camilabga/boberto/CAD/sharp.SLDPRT

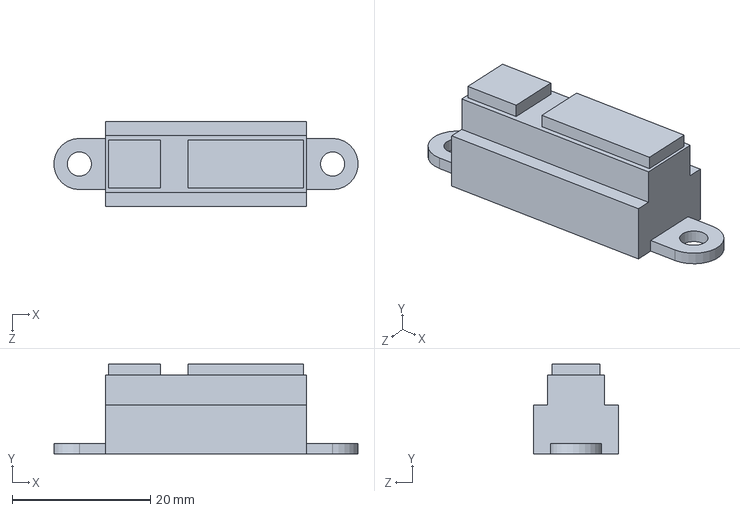
[picture p17: CAD file, 2019-10-31]
CAD/sharp.SLDPRT
43.9 x 13.0 x 12.3 mm
