camilabga/boberto/CAD/suporte barras base.SLDPRT

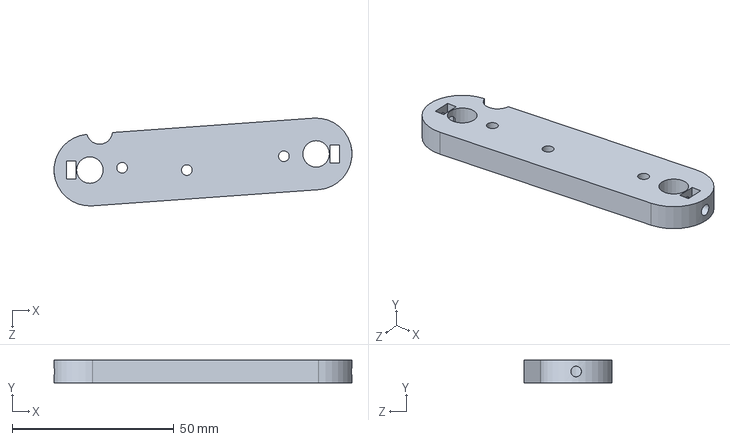
[picture p18: CAD file, 2019-10-31]
CAD/suporte barras base.SLDPRT
92.2 x 7.00 x 27.1 mm
