camilabga/boberto/CAD/suporte fim de curso.SLDPRT

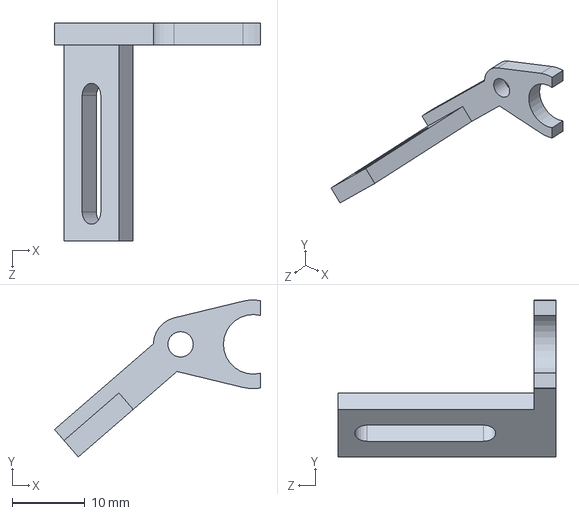
[picture p19: CAD file, 2019-10-31]
CAD/suporte fim de curso.SLDPRT
28.4 x 21.6 x 30.0 mm
