camilabga/boberto/CAD/polia com rolamento.SLDPRT

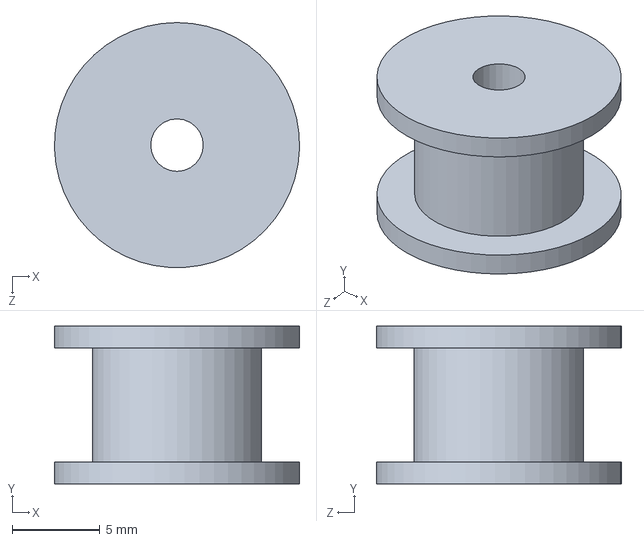
[picture p20: CAD file, 2019-10-31]
CAD/polia com rolamento.SLDPRT
14.0 x 9.00 x 14.0 mm
