camilabga/boberto/CAD/nema17 (30mm altura).SLDPRT

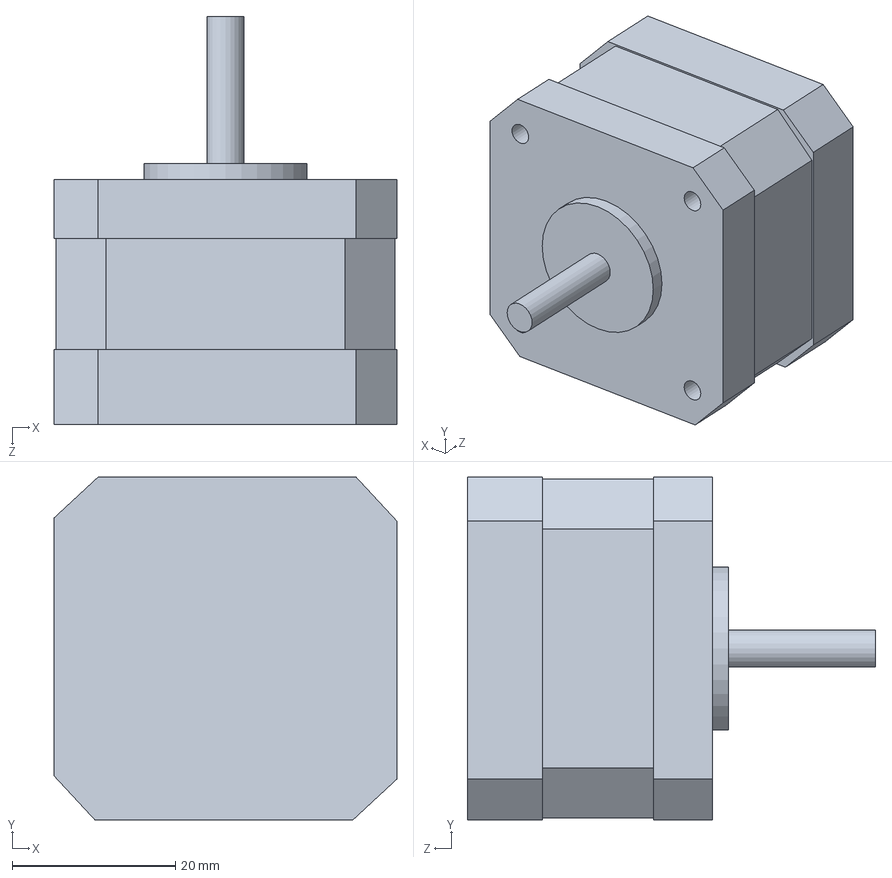
[picture p21: CAD file, 2019-10-31]
CAD/nema17 (30mm altura).SLDPRT
42.0 x 42.0 x 50.0 mm
