camilabga/boberto/CAD/chassis meio.SLDPRT

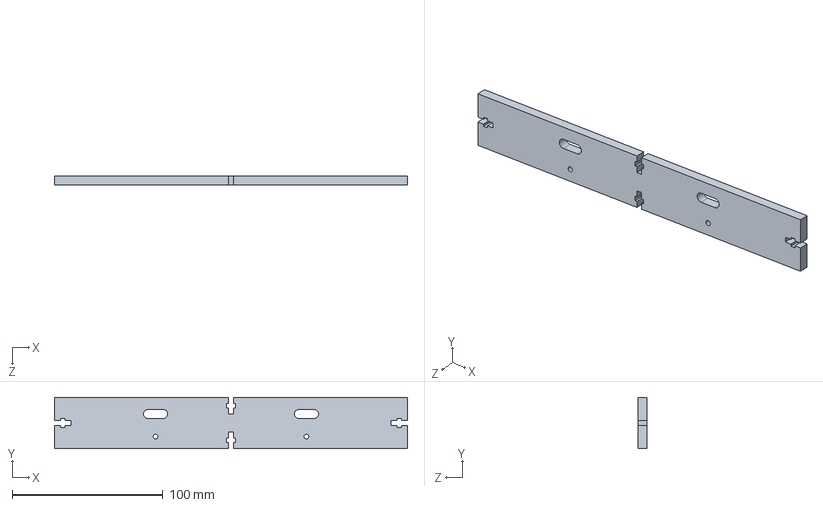
[picture p22: CAD file, 2019-10-31]
CAD/chassis meio.SLDPRT
234.0 x 34.0 x 6.00 mm
