camilabga/boberto/CAD/Servo 9g.SLDPRT

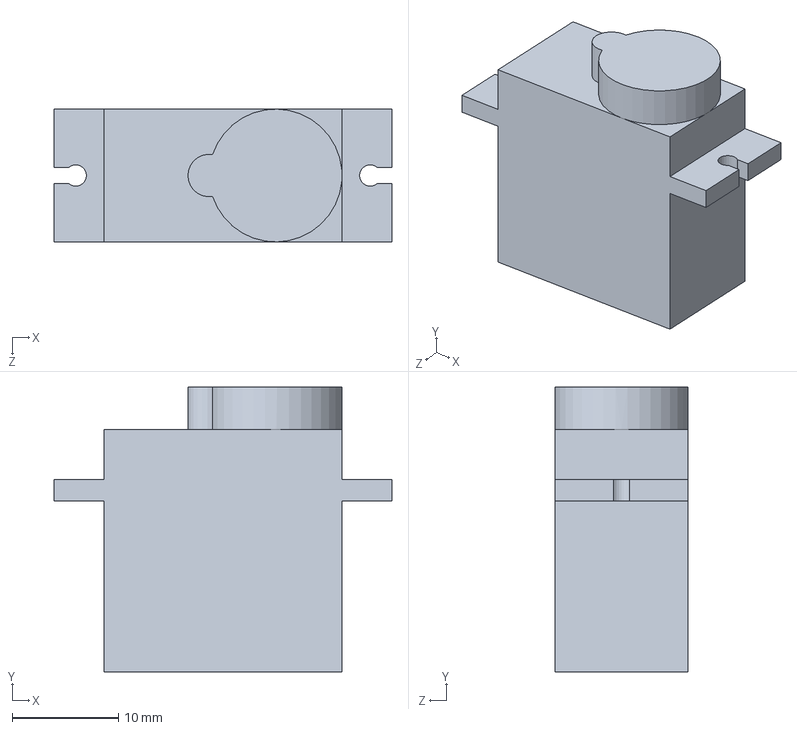
[picture p23: CAD file, 2019-10-31]
CAD/Servo 9g.SLDPRT
31.8 x 26.8 x 12.5 mm
