camilabga/boberto/CAD/motor N20.SLDPRT

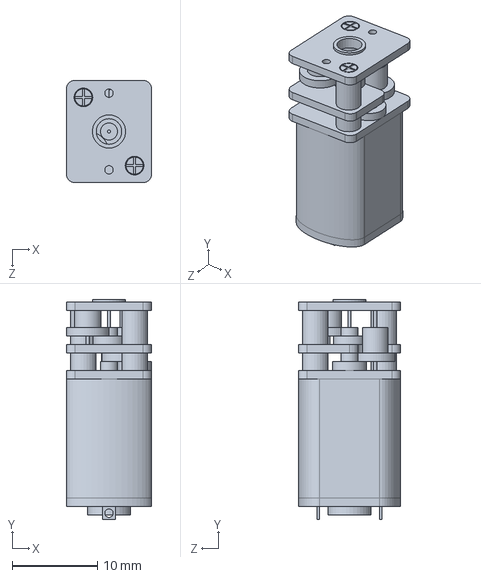
[picture p24: CAD file, 2019-10-31]
CAD/motor N20.SLDPRT
10.0 x 25.8 x 12.0 mm
