camilabga/boberto/CAD/apoio container.SLDPRT

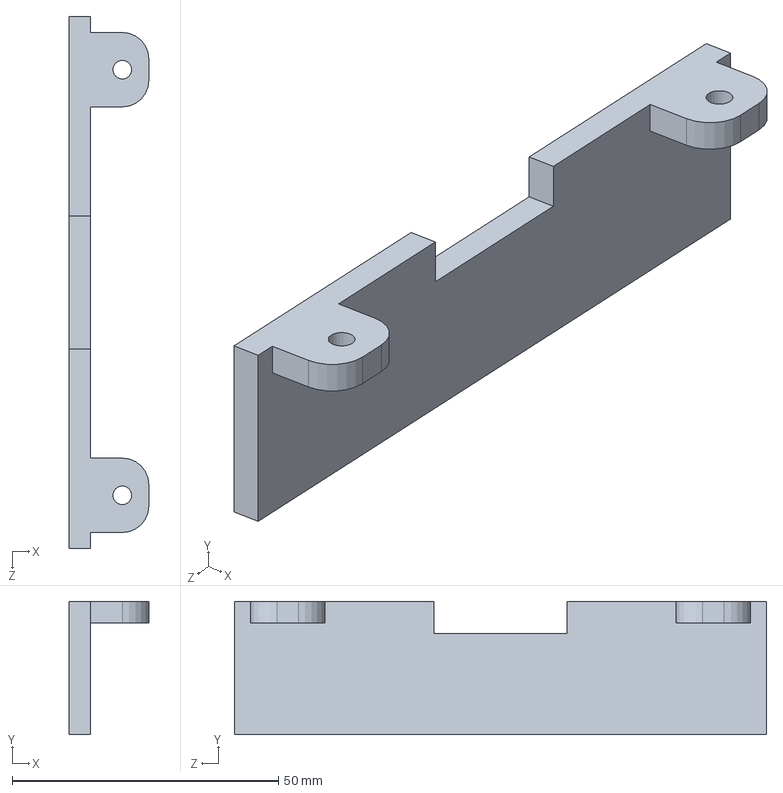
[picture p25: CAD file, 2019-10-31]
CAD/apoio container.SLDPRT
15.0 x 25.0 x 100.0 mm
