camilabga/boberto/CAD/chassis direita.SLDPRT

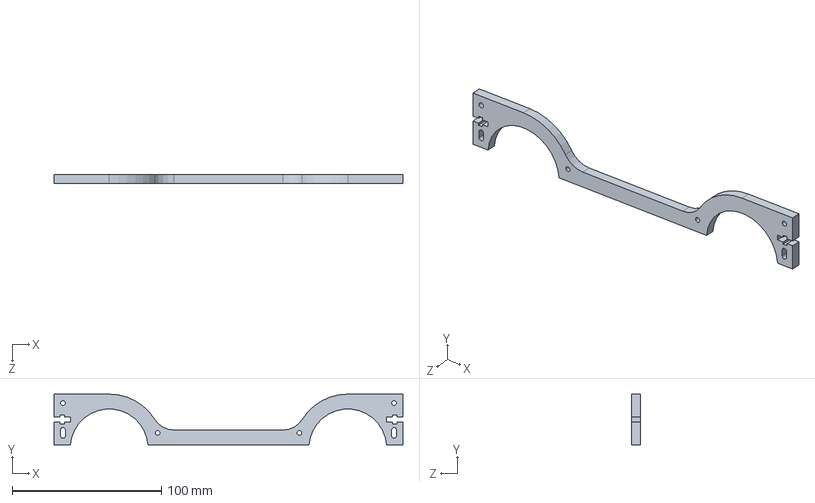
[picture p26: CAD file, 2019-10-31]
CAD/chassis direita.SLDPRT
234.0 x 34.1 x 6.00 mm
