camilabga/boberto/CAD/contrapeso.SLDPRT

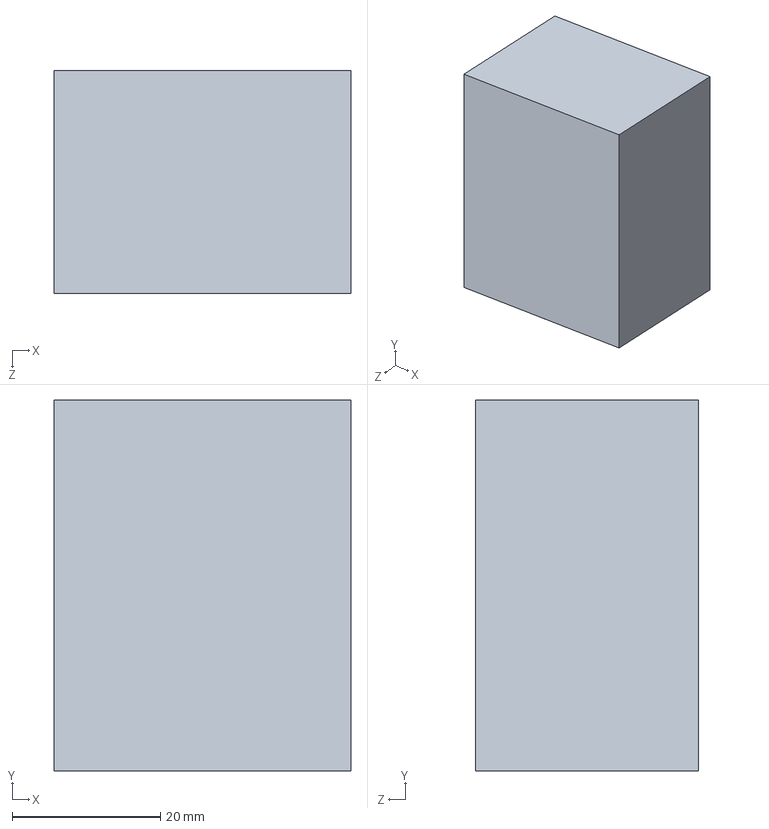
[picture p27: CAD file, 2019-10-31]
CAD/contrapeso.SLDPRT
40.0 x 50.0 x 30.0 mm
