camilabga/boberto/CAD/PCB + arduino.SLDPRT

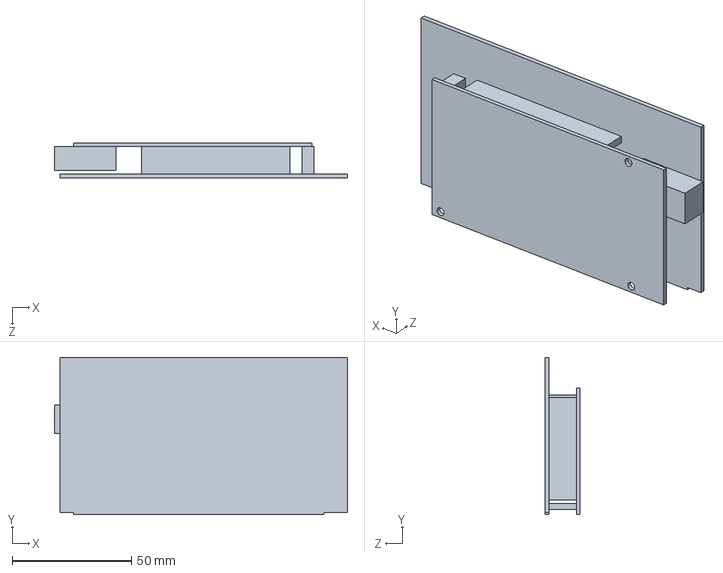
[picture p28: CAD file, 2019-10-31]
CAD/PCB + arduino.SLDPRT
122.9 x 65.9 x 14.8 mm
