camilabga/boberto/CAD/suporte correia.SLDPRT

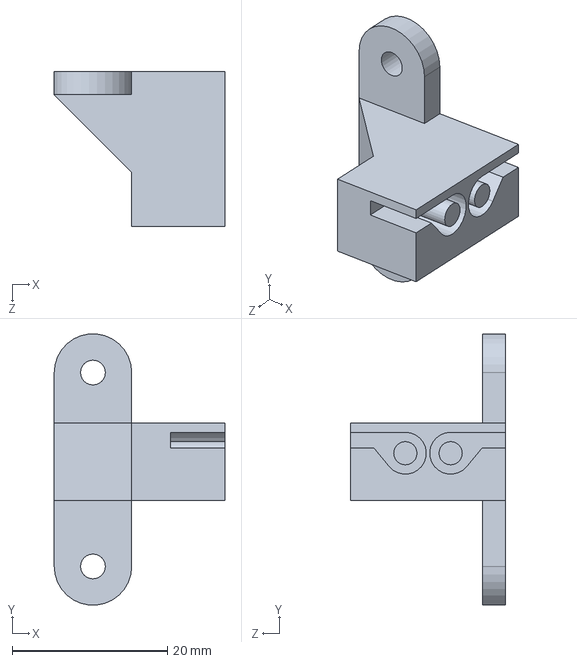
[picture p29: CAD file, 2019-10-31]
CAD/suporte correia.SLDPRT
22.0 x 34.9 x 20.0 mm
