camilabga/boberto/CAD/suporte sensores laterais.SLDPRT

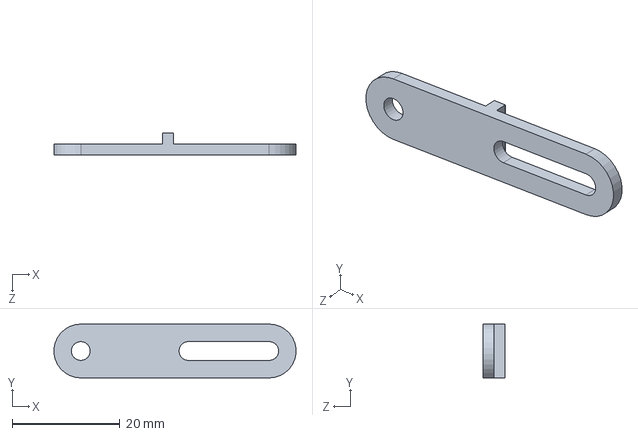
[picture p30: CAD file, 2019-10-31]
CAD/suporte sensores laterais.SLDPRT
44.9 x 10.0 x 4.00 mm
