camilabga/boberto/CAD/chassis.SLDPRT

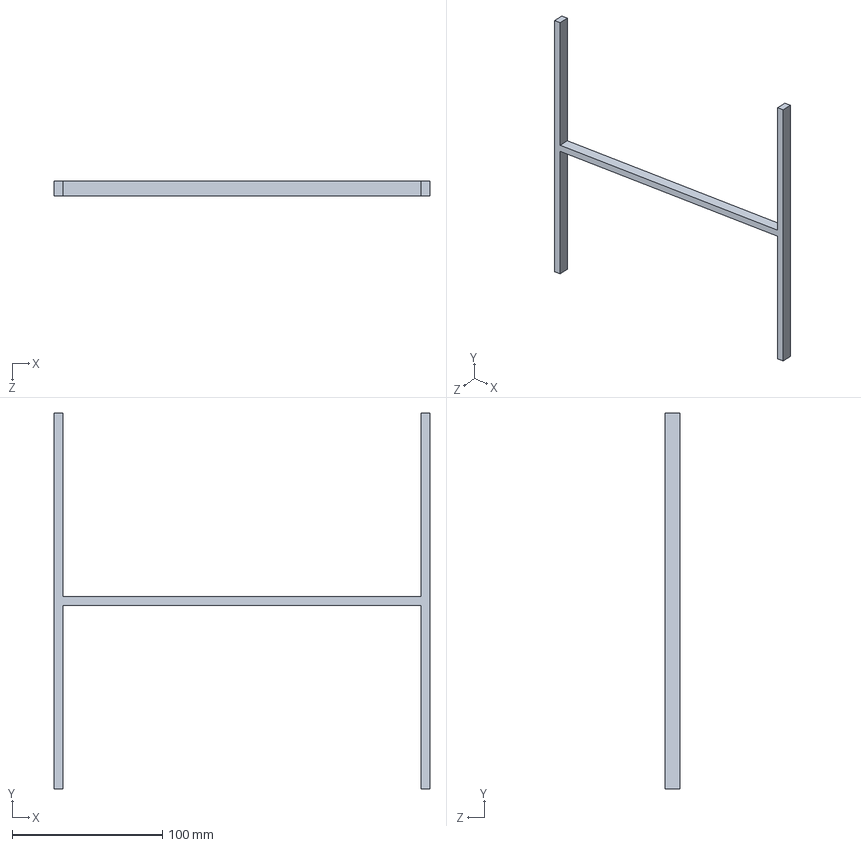
[picture p31: CAD file, 2019-10-31]
CAD/chassis.SLDPRT
250.0 x 250.0 x 10.0 mm
