camilabga/boberto/CAD/suporte barras topo.SLDPRT

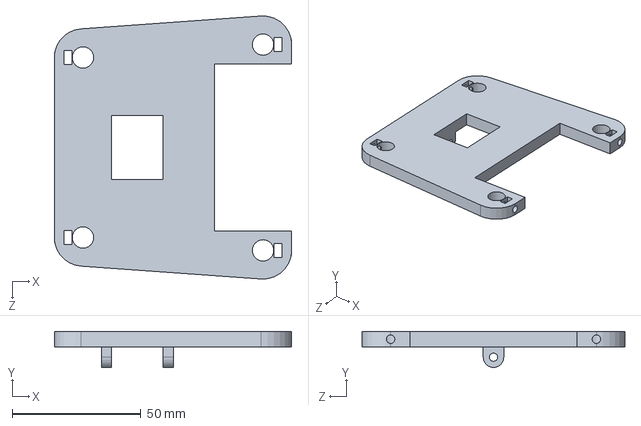
[picture p32: CAD file, 2019-10-31]
CAD/suporte barras topo.SLDPRT
92.3 x 14.0 x 102.2 mm
