camilabga/boberto/CAD/chao.SLDPRT

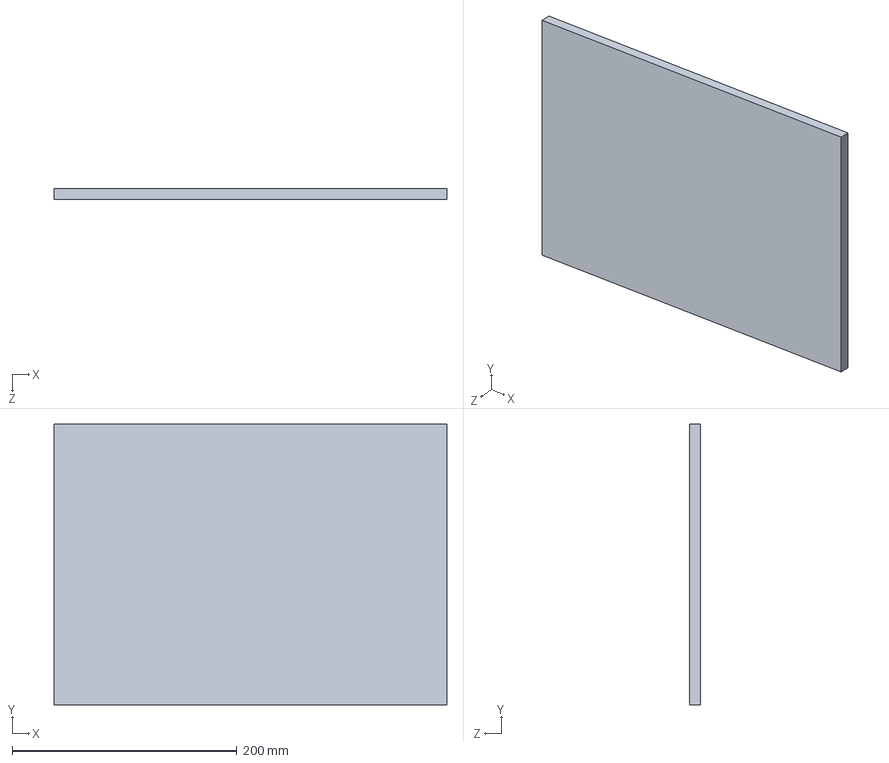
[picture p33: CAD file, 2019-10-31]
CAD/chao.SLDPRT
350.0 x 250.0 x 10.1 mm
