camilabga/boberto/CAD/sparkfun color sensor.SLDPRT

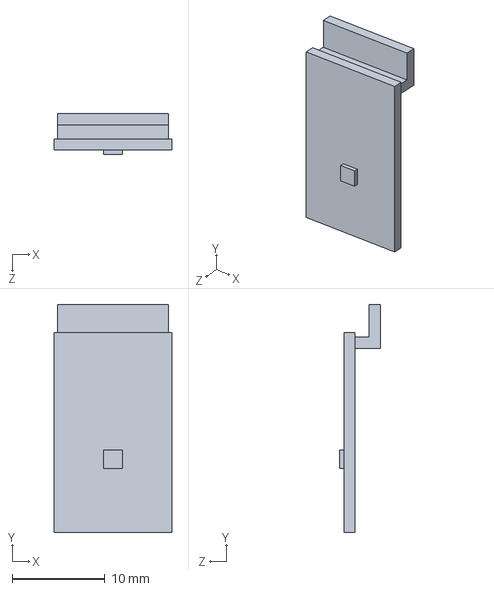
[picture p34: CAD file, 2019-10-31]
CAD/sparkfun color sensor.SLDPRT
12.7 x 24.6 x 4.47 mm
