camilabga/boberto/CAD/motor 12v com reducao e encoder.SLDPRT

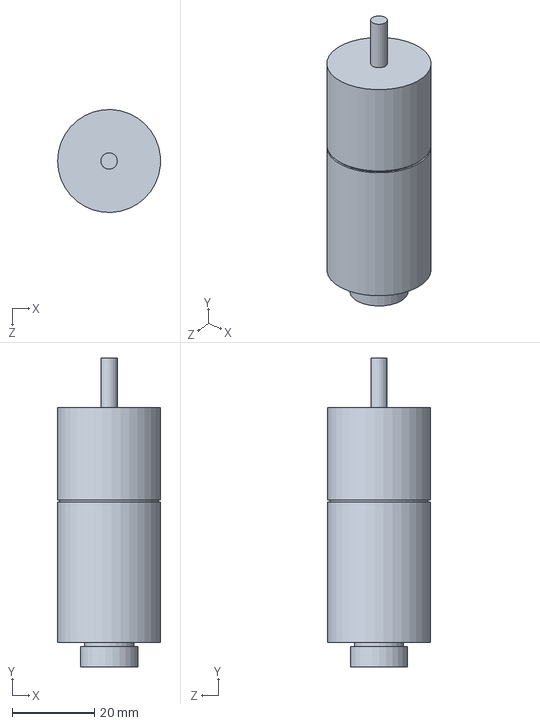
[picture p35: CAD file, 2019-10-31]
CAD/motor 12v com reducao e encoder.SLDPRT
24.9 x 75.0 x 25.0 mm
