camilabga/boberto/CAD/segundo andar.SLDPRT

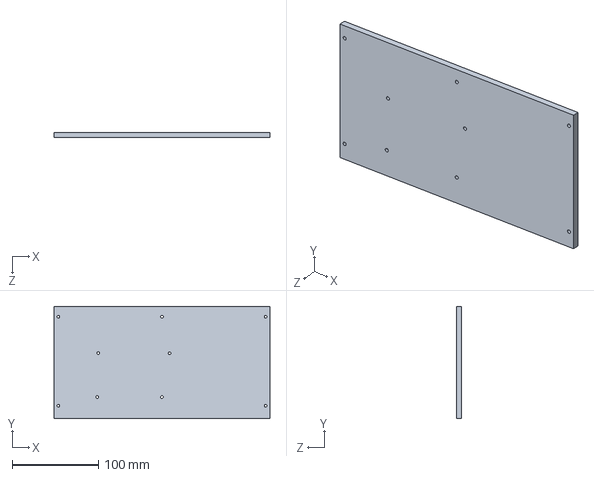
[picture p36: CAD file, 2019-10-31]
CAD/segundo andar.SLDPRT
250.0 x 130.0 x 6.00 mm
