camilabga/boberto/CAD/extensor sensor laser.SLDPRT

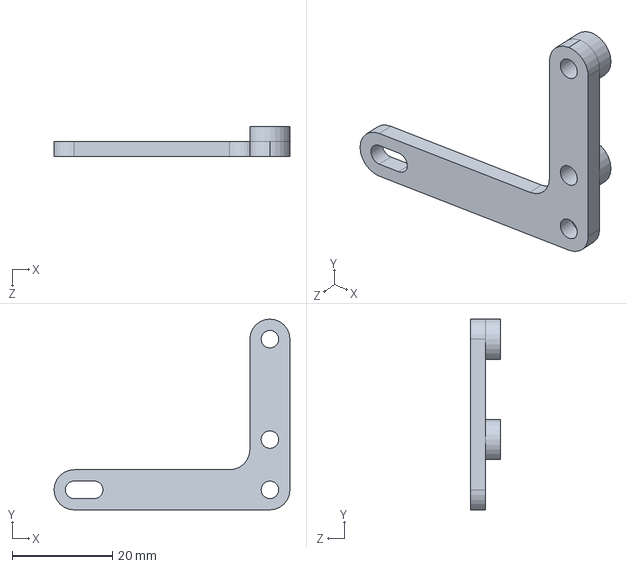
[picture p37: CAD file, 2019-10-31]
CAD/extensor sensor laser.SLDPRT
47.0 x 38.0 x 6.00 mm
