camilabga/boberto/CAD/correia.SLDPRT

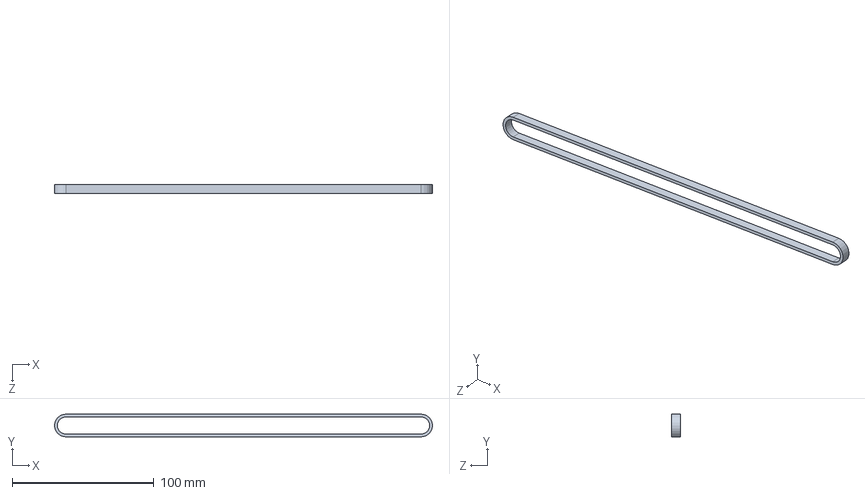
[picture p38: CAD file, 2019-10-31]
CAD/correia.SLDPRT
266.5 x 16.0 x 6.00 mm
