camilabga/boberto/CAD/chassis reforco.SLDPRT

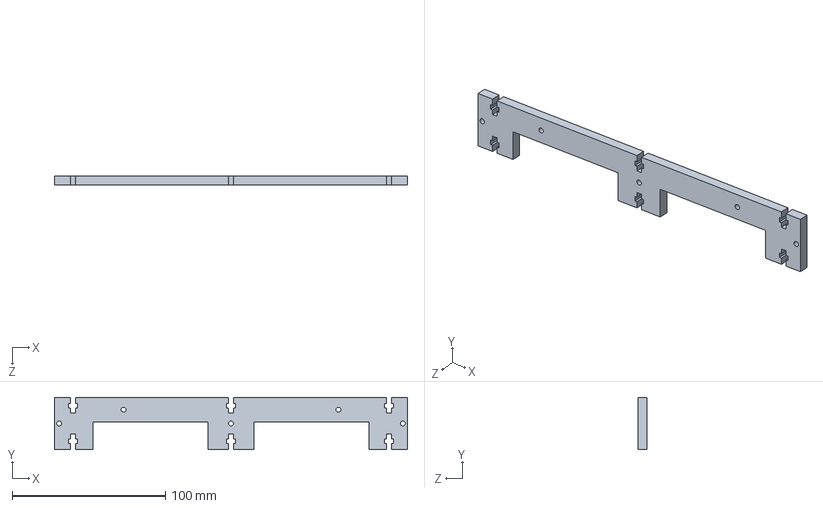
[picture p39: CAD file, 2019-10-31]
CAD/chassis reforco.SLDPRT
230.0 x 34.0 x 6.00 mm
