camilabga/boberto/CAD/base.SLDPRT

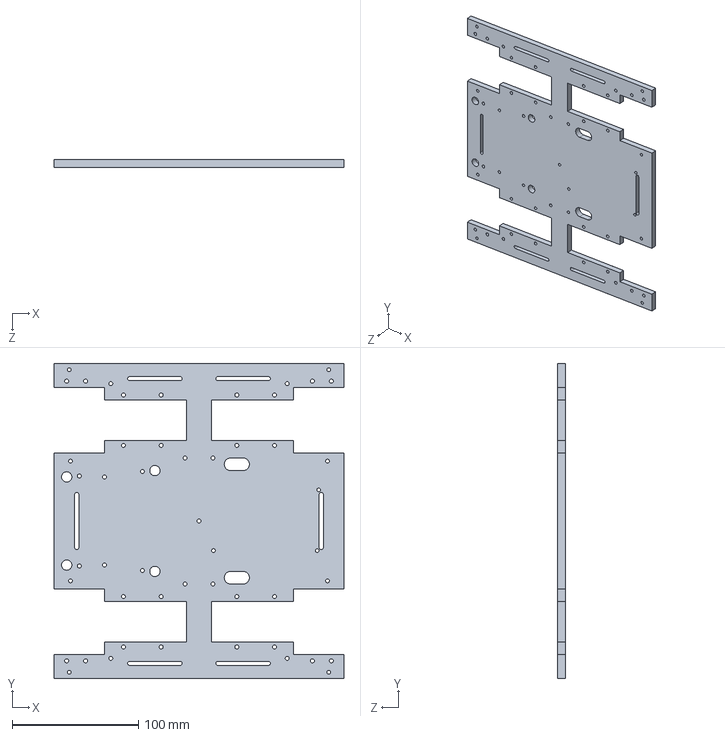
[picture p40: CAD file, 2019-10-31]
CAD/base.SLDPRT
230.0 x 250.0 x 6.00 mm
