camilabga/boberto/CAD/sensor de azul.SLDPRT

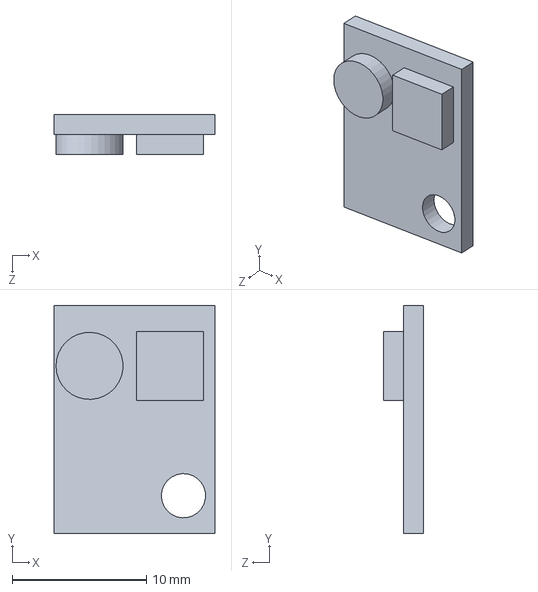
[picture p41: CAD file, 2019-10-31]
CAD/sensor de azul.SLDPRT
12.0 x 17.0 x 3.00 mm
