camilabga/boberto/CAD/motor n20 trava.SLDPRT

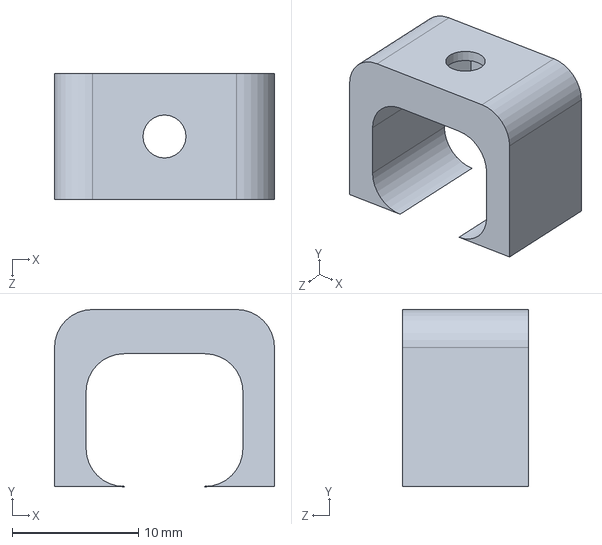
[picture p42: CAD file, 2019-10-31]
CAD/motor n20 trava.SLDPRT
17.4 x 14.0 x 10.0 mm
