camilabga/boberto/CAD/suporte motor.SLDPRT

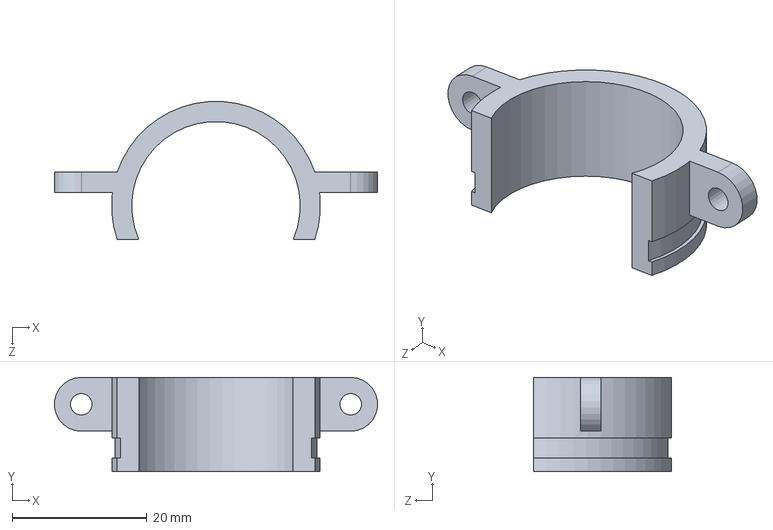
[picture p43: CAD file, 2019-10-31]
CAD/suporte motor.SLDPRT
47.9 x 14.0 x 20.5 mm
