camilabga/boberto/CAD/cremalheira.SLDPRT

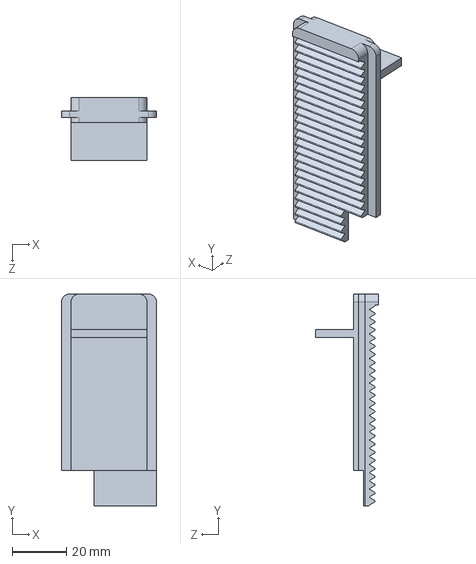
[picture p44: CAD file, 2019-10-31]
CAD/cremalheira.SLDPRT
35.0 x 78.0 x 23.3 mm
