camilabga/boberto/CAD/suporte contra peso.SLDPRT

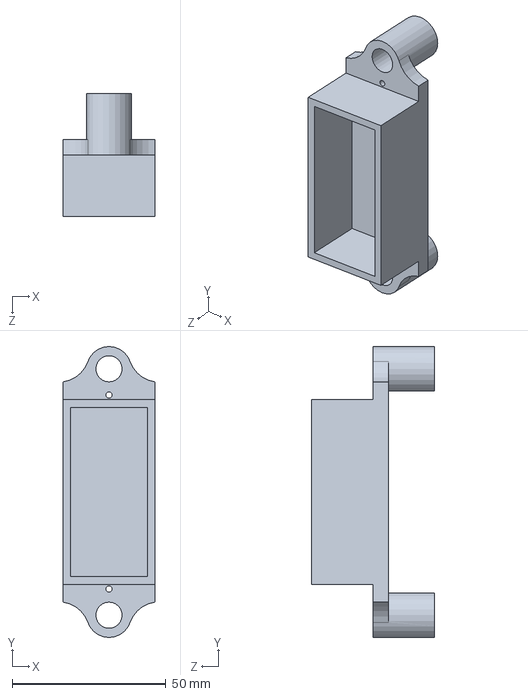
[picture p45: CAD file, 2019-10-31]
CAD/suporte contra peso.SLDPRT
30.0 x 94.5 x 40.0 mm
