camilabga/boberto/CAD/polia gt2.SLDPRT

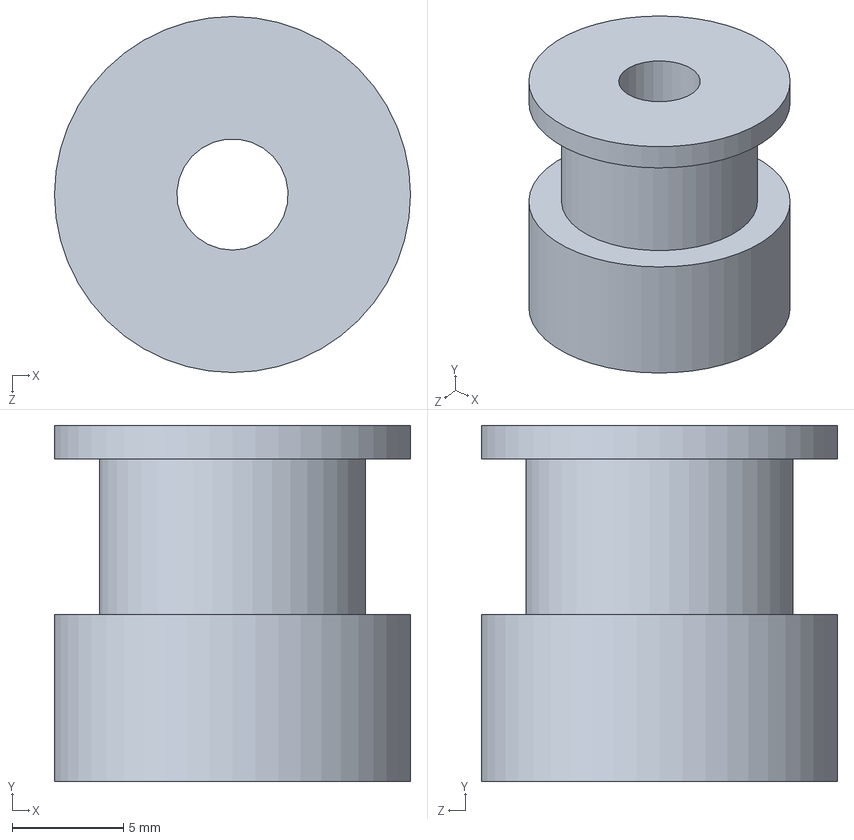
[picture p46: CAD file, 2019-10-31]
CAD/polia gt2.SLDPRT
16.0 x 16.0 x 16.0 mm
