camilabga/boberto/src/Arena.hpp

#ifndef ARENA_HPP
#define ARENA_HPP

#include <Arduino.h>

enum CONTAINER_SIDE {
	clawSide = 1,
	otherSide = 0
};

struct Ship {
	uint8_t currentPile = 0;
	uint8_t currentHeight = 1;

	void increment () {
		currentHeight++;

		if (currentHeight == 7) {
			currentPile++;
			currentHeight = 1;
		}
	}
};

struct ContainerZone {
	uint8_t clawSide[2] = {4, 4};
	uint8_t otherSide[2] = {4, 4};

	uint8_t locked[2] = {0, 0};

	bool isEmpty(uint8_t side) {
		if (side) {
			if (locked[0] and locked[1]) 
                return true;
			else if (locked[0] and clawSide[1])
				return false;
			else if (locked[0] and !clawSide[1])
				return true;
			else if (!clawSide[0] and locked[1])
				return true;
			else if (!clawSide[0] and clawSide[1])
				return false;
			else if (!clawSide[0] and !clawSide[1])
				return true;
			else if (clawSide[0] and clawSide[1])
				return false;
			else 
                return true;

		} else {
			if (otherSide[1] == 0) 
                return true;
			else 
                return false;
		}
	}

	uint8_t getHeight(uint8_t side) {
		if (side) {
			if (!clawSide[0] or locked[0]) 
                return clawSide[1];

			return clawSide[0];

		} else {
			if (!clawSide[0] or locked[0]) 
                return otherSide[1];
			
            return otherSide[0];
		}
	}

	void updateHeight(uint8_t side) {
		if (side) {
			if (!clawSide[0] or locked[0]) {
				locked[0] = 1;
				clawSide[1] -= 1;
			} else
				clawSide[0] -= 1;
		
		} else {
			if (otherSide[0] == 0)
				otherSide[1]--;
			else
				otherSide[0]--;	
		}
	}

	void lockPile() {

		if (clawSide[0]) {
			if (!locked[0])
				locked[0] = 1;
			else 
				locked[1] = 1;
		} else {
			locked[1] = 1;
		}
			
	}

	uint8_t isLocked() {
		return locked[0];
	}

	uint8_t getCurrentPile() {
		if ((!clawSide[0] or locked[0]) and (!clawSide[1] or locked[1]))
			return 1;
		else
			return 0;
	}

};

/*
	side: true ==> green | blue
		  false ==> blue | green
*/

struct Arena {
	ContainerZone containers[3];
	Ship greenShip;
	Ship blueShip;

	bool side = true;
};

#endif // ARENA_HPP
