camilabga/boberto/src/Claw.hpp

#ifndef CLAW_HPP
#define CLAW_HPP

#include <Arduino.h>

class Claw {
    private:
        // Pinos do motor de passo
        uint8_t setPin; 
        uint8_t dirPin;
        uint8_t enable;
        
        // Pinos do motor DC
        uint8_t motorPin1;
        uint8_t motorPin2;

        // Pino do fins de curso
        uint8_t endStopPin;
        uint8_t endStopPin2;

        // Altura atual da garra
        float height;

    public:
        Claw(uint8_t _setPin, uint8_t _dirPin, uint8_t _enable, uint8_t _motorPin1, uint8_t _motorPin2, uint8_t _endStopPin, uint8_t _endStopPin2);
        ~Claw();

        void goUp();
        void goDown();

        void goHome();

        void goToContainer(float container);
        void catchContainer(uint8_t container);

        void extend();
        void retract();
        void ajustContainer();
        void stop();
    
};

#endif // CLAW_HPP
